74ls00/Battery-Tester-1.1/hw/png/200.png

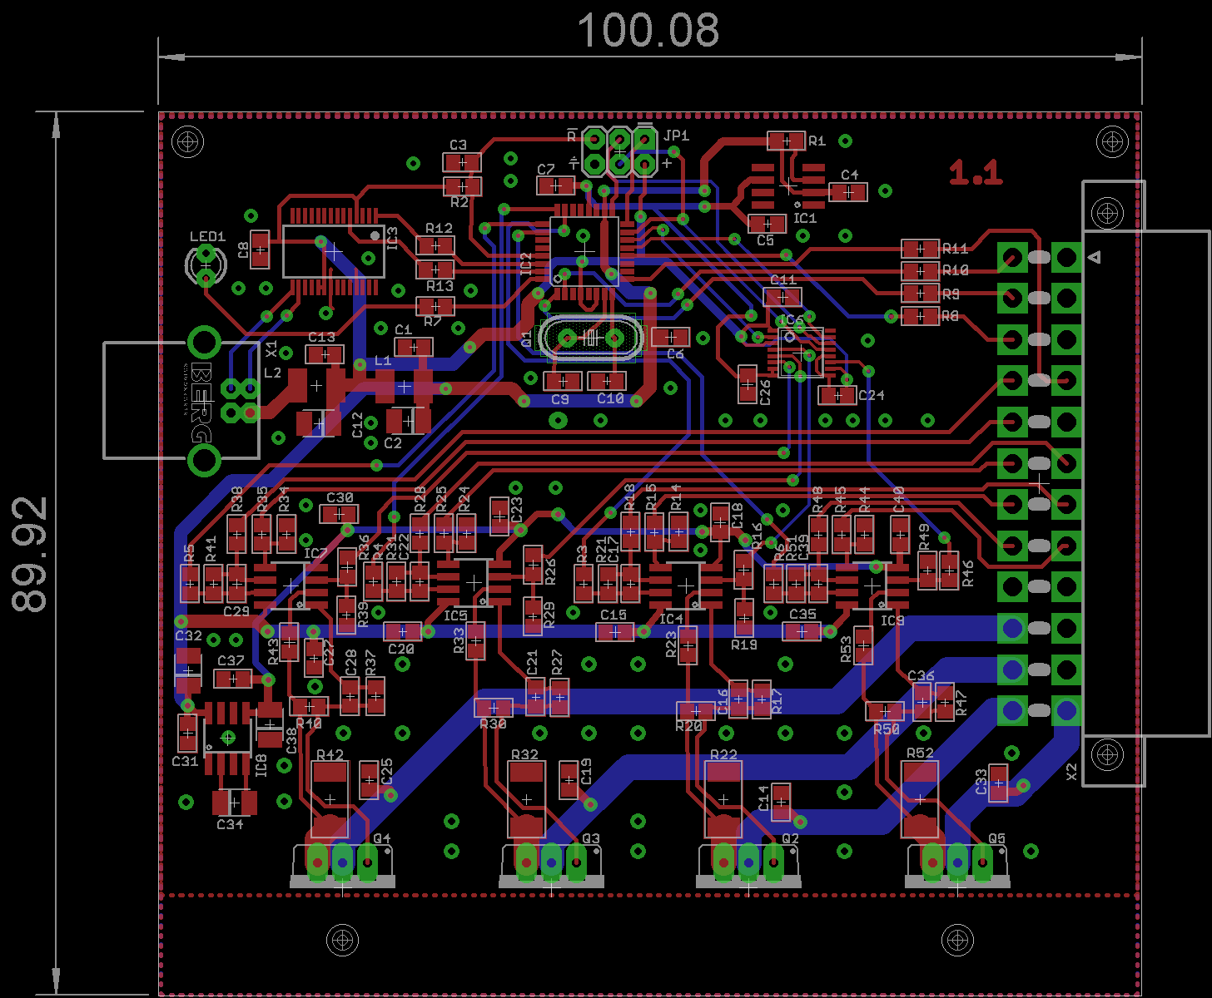
hw/png/200.png
