74ls00/Battery-Tester-1.1/sw/src/Project1.cpp

//---------------------------------------------------------------------------

#include <vcl.h>
#pragma hdrstop
#include <tchar.h>
//---------------------------------------------------------------------------








USEFORM("Unit2.cpp", Form2);
USEFORM("Unit4.cpp", Form4);
USEFORM("Unit1.cpp", Form1);
//---------------------------------------------------------------------------
WINAPI _tWinMain(HINSTANCE, HINSTANCE, LPTSTR, int)
{
	try
	{
		Application->Initialize();
		Application->MainFormOnTaskBar = true;
		Application->CreateForm(__classid(TForm1), &Form1);
		Application->CreateForm(__classid(TForm2), &Form2);
		Application->CreateForm(__classid(TForm4), &Form4);
		Application->Run();
	}
	catch (Exception &exception)
	{
		Application->ShowException(&exception);
	}
	catch (...)
	{
		try
		{
			throw Exception("");
		}
		catch (Exception &exception)
		{
			Application->ShowException(&exception);
		}
	}
	return 0;
}
//---------------------------------------------------------------------------
