74ls00/Battery-Tester-1.1/sw/src/Unit2.cpp

//---------------------------------------------------------------------------

#include <vcl.h>
#pragma hdrstop

#include "Unit2.h"
//---------------------------------------------------------------------------
#pragma package(smart_init)
#pragma link "cgauges"
#pragma resource "*.dfm"
TForm2 *Form2;
//---------------------------------------------------------------------------
__fastcall TForm2::TForm2(TComponent* Owner)
	: TForm(Owner)
{
}
//---------------------------------------------------------------------------
