74ls00/Battery-Tester-1.1/sw/src/Unit2.h

//---------------------------------------------------------------------------

#ifndef Unit2H
#define Unit2H
//---------------------------------------------------------------------------
#include <Classes.hpp>
#include <Controls.hpp>
#include <StdCtrls.hpp>
#include <Forms.hpp>
#include "cgauges.h"
//---------------------------------------------------------------------------
class TForm2 : public TForm
{
__published:	// IDE-managed Components
	TCGauge *CGauge1;
private:	// User declarations
public:		// User declarations
	__fastcall TForm2(TComponent* Owner);
};
//---------------------------------------------------------------------------
extern PACKAGE TForm2 *Form2;
//---------------------------------------------------------------------------
#endif
