74ls00/Battery-Tester-1.1/sw/src/fft.h

//---------------------------------------------------------------------------

#ifndef fftH
#define fftH
//---------------------------------------------------------------------------
void four1(float data[], unsigned long nn, int isign);
#endif
